mikepdiy/Macro-Keyboard-with-Encoders/Schematic/KB_Board_schematic.sch

## EAGLE design Schematic/KB_Board_schematic.sch (2021-04-27)

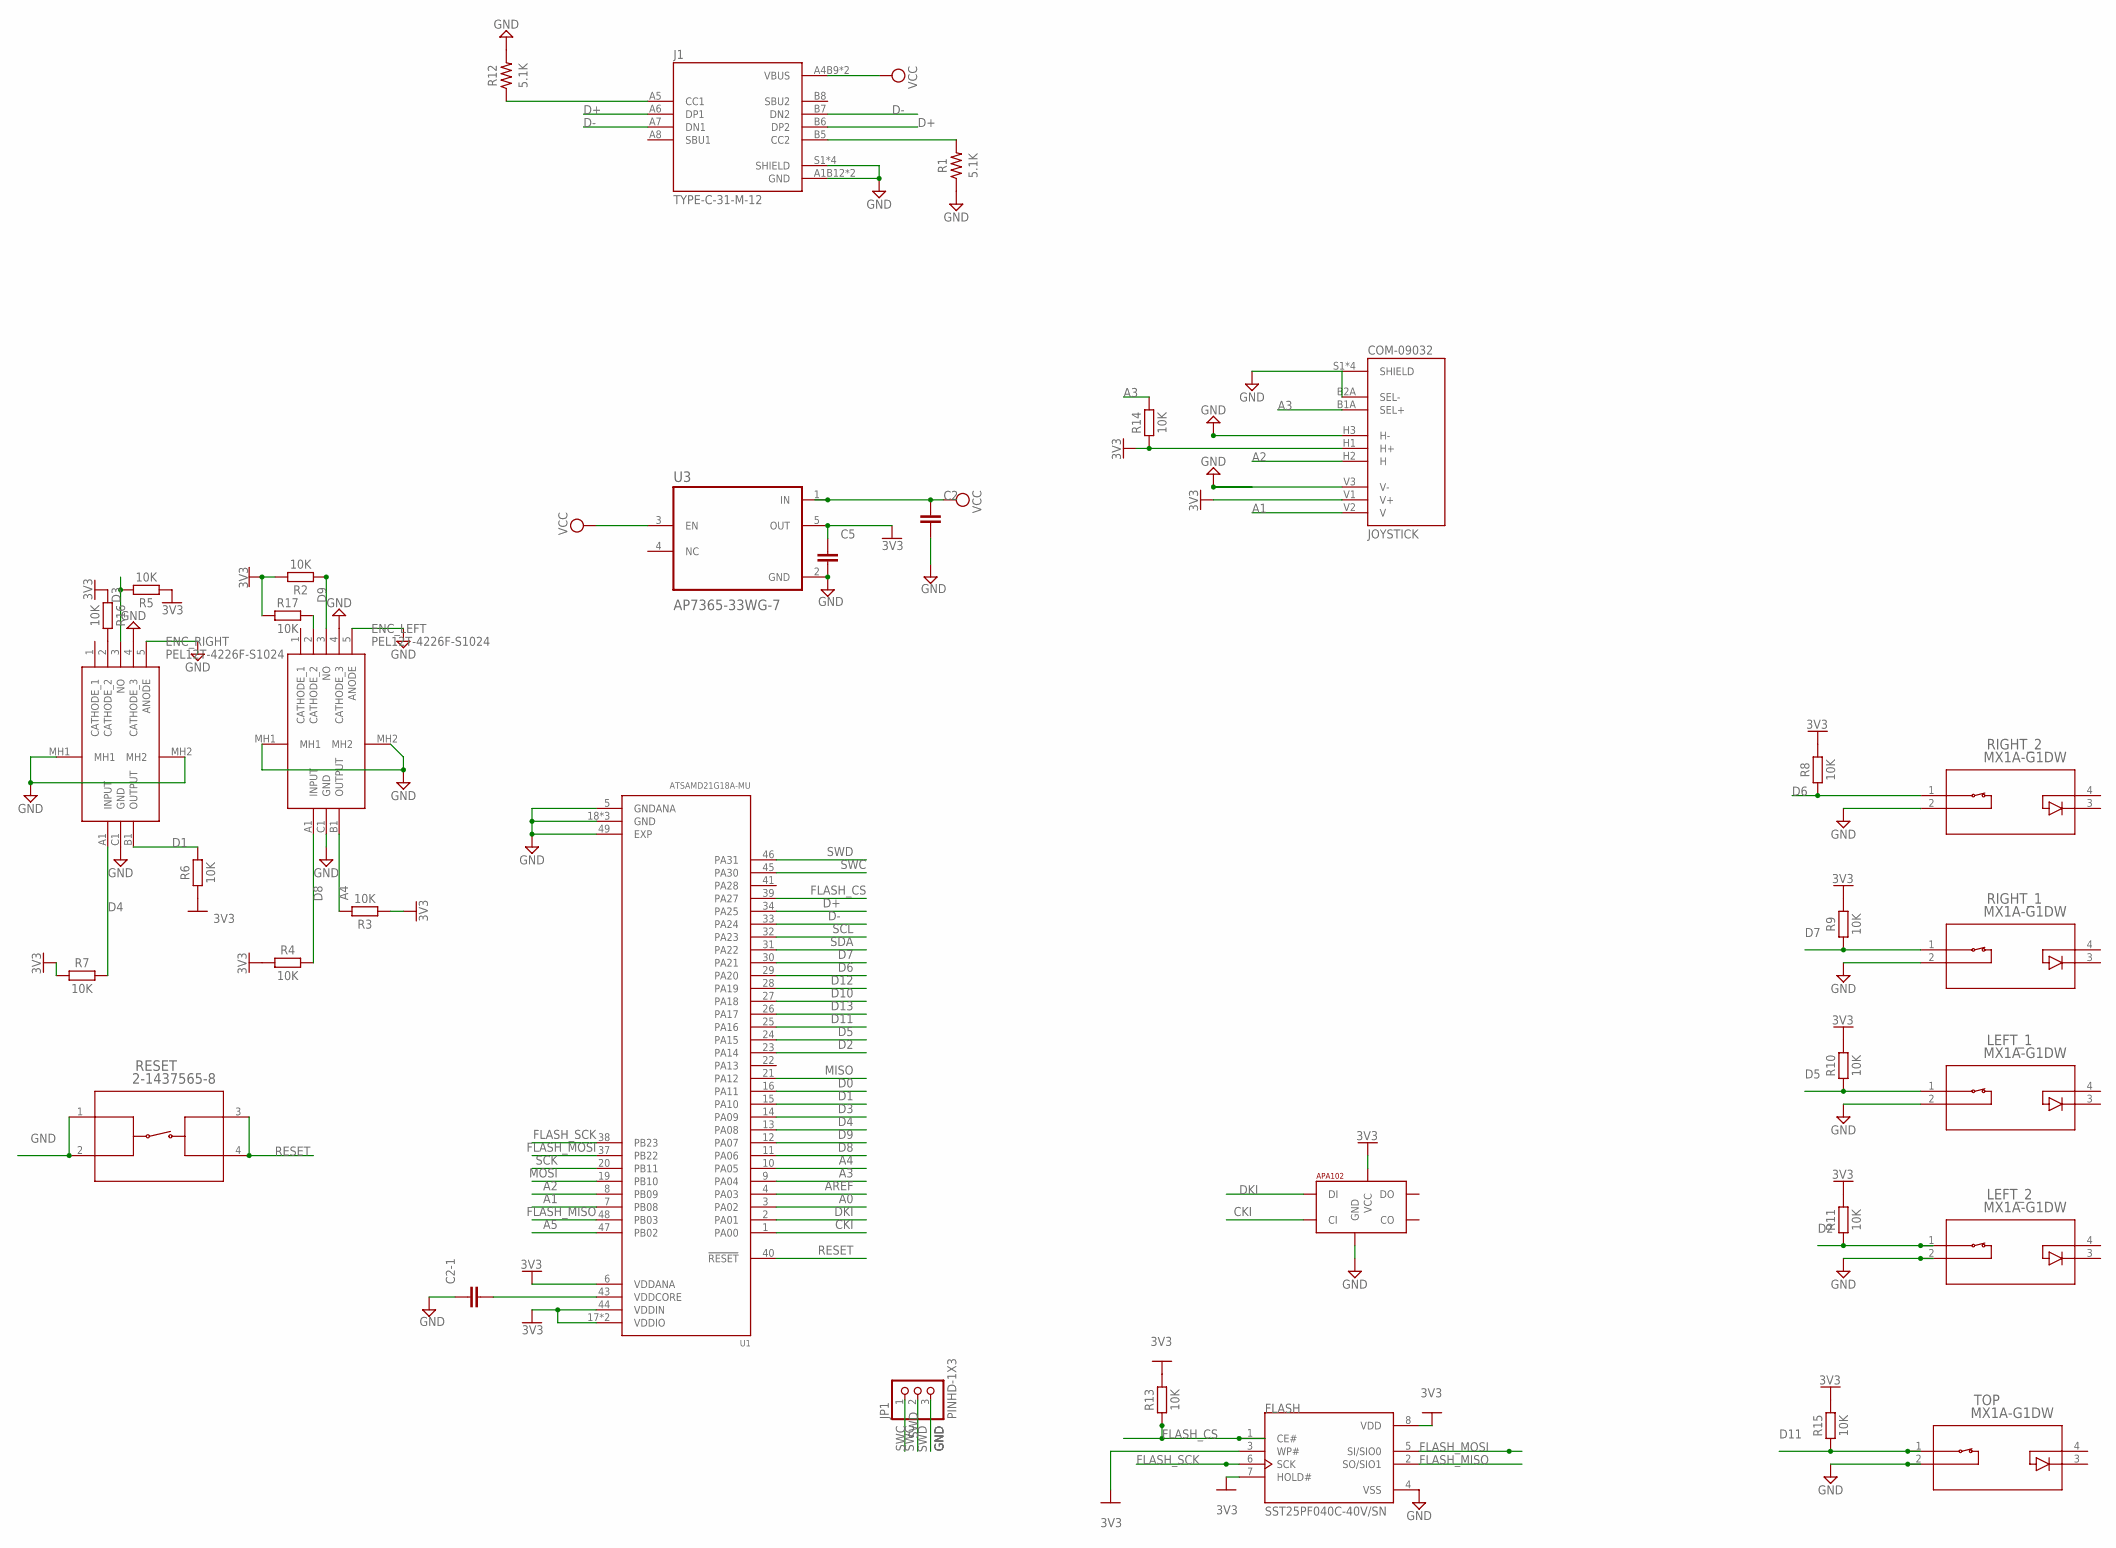
[picture p17: schematic KB_Board_schematic.sch]

Parts:
C2, C2-1, C5: C_CHIP-0805(2012-METRIC); CAPC2012X110
ENC_LEFT: PEL12T-4226F-S1024; PEL12T4226FS1024
ENC_RIGHT: PEL12T-4226F-S1024; PEL12T4226FS1024
FLASH: SST25PF040C-40V/SN; SOIC8
J1: TYPE-C-31-M-12; HRO_TYPE-C-31-M-12
JOYSTICK: COM-09032; XDCR_COM-09032
JP1: PINHD-1X3; 1X03
LEFT_1, LEFT_2: MX1A-G1DW; MX1A-G1DW_CHY
R1, R12: 5.1K; RESC1005X40
R2, R3, R4, R5, R6, R7, R8, R9, R10, R11, R13, R14, R15, R16, R17: 10K; RESC1608X60
RESET: 2-1437565-8; SW4_2-1437565-7
RIGHT_1, RIGHT_2: MX1A-G1DW; MX1A-G1DW_CHY
TOP: MX1A-G1DW; MX1A-G1DW_CHY
U1: ATSAMD21G18A-MU; QFN50P700X700X90-49N
U3: AP7365-33WG-7; SOT95P285X140-5N
U$1: APA1022020; APA102_2020

Connections:
3V3: C5.1, FLASH.3 (WP#), FLASH.7 (HOLD#), FLASH.8 (VDD), JOYSTICK.H1 (H+), JOYSTICK.V1 (V+), R2.2, R3.1, R4.1, R5.2, R6.1, R7.1, R8.2, R9.2, R10.2, R11.2, R13.2, R14.1, R15.2, R16.2, R17.2, U1.6 (VDDANA), U1.17 (VDDIO), U1.44 (VDDIN), U3.5 (OUT), U$1.V_CC (VCC)
A0: U1.3 (PA02)
A1: JOYSTICK.V2 (V), U1.7 (PB08)
A2: JOYSTICK.H2 (H), U1.8 (PB09)
A3: JOYSTICK.B1A (SEL+), R14.2, U1.9 (PA04)
A4: ENC_LEFT.B1 (OUTPUT), R3.2, U1.10 (PA05)
A5: U1.47 (PB02)
AREF: U1.4 (PA03)
CKI: U1.1 (PA00), U$1.C_IN (CI)
D0: U1.16 (PA11)
D1: ENC_RIGHT.B1 (OUTPUT), R6.2, U1.15 (PA10)
D2: LEFT_2.1, R11.1, U1.23 (PA14)
D3: ENC_RIGHT.3 (NO), R5.1, U1.14 (PA09)
D4: ENC_RIGHT.A1 (INPUT), R7.2, U1.13 (PA08)
D5: LEFT_1.1, R10.1, U1.24 (PA15)
D6: R8.1, RIGHT_2.1, U1.29 (PA20)
D7: R9.1, RIGHT_1.1, U1.30 (PA21)
D8: ENC_LEFT.A1 (INPUT), R4.2, U1.11 (PA06)
D9: ENC_LEFT.3 (NO), R2.1, U1.12 (PA07)
D10: U1.27 (PA18)
D11: R15.1, TOP.1, U1.25 (PA16)
D12: U1.28 (PA19)
D13: U1.26 (PA17)
D+: J1.A6 (DP1), J1.B6 (DP2), U1.34 (PA25)
D-: J1.A7 (DN1), J1.B7 (DN2), U1.33 (PA24)
DKI: U1.2 (PA01), U$1.D_IN (DI)
FLASH_CS: FLASH.1 (CE#), R13.1, U1.39 (PA27)
FLASH_MISO: FLASH.2 (SO/SIO1), U1.48 (PB03)
FLASH_MOSI: FLASH.5 (SI/SIO0), U1.37 (PB22)
FLASH_SCK: FLASH.6 (SCK), U1.38 (PB23)
GND: C2.2, C2-1.1, C5.2, ENC_LEFT.4 (CATHODE_3), ENC_LEFT.5 (ANODE), ENC_LEFT.C1 (GND), ENC_LEFT.MH1, ENC_LEFT.MH2, ENC_RIGHT.4 (CATHODE_3), ENC_RIGHT.5 (ANODE), ENC_RIGHT.C1 (GND), ENC_RIGHT.MH1, ENC_RIGHT.MH2, FLASH.4 (VSS), J1.A1B12 (GND), J1.S1 (SHIELD), JOYSTICK.B2A (SEL-), JOYSTICK.H3 (H-), JOYSTICK.S1 (SHIELD), JOYSTICK.V3 (V-), JP1.3, LEFT_1.2, LEFT_2.2, R1.1, R12.2, RESET.1, RESET.2, RIGHT_1.2, RIGHT_2.2, TOP.2, U1.5 (GNDANA), U1.18 (GND), U1.49 (EXP), U3.2 (GND), U$1.GND
MISO: U1.21 (PA12)
MOSI: U1.19 (PB10)
unnamed: C2-1.2, U1.43 (VDDCORE)
unnamed: J1.B5 (CC2), R1.2
unnamed: J1.A5 (CC1), R12.1
unnamed: ENC_RIGHT.2 (CATHODE_2), R16.1
unnamed: ENC_LEFT.2 (CATHODE_2), R17.1
RESET: RESET.3, RESET.4, U1.40 (!RESET)
SCK: U1.20 (PB11)
SCL: U1.32 (PA23)
SDA: U1.31 (PA22)
SWC: JP1.1, U1.45 (PA30)
SWD: JP1.2, U1.46 (PA31)
VCC: C2.1, J1.A4B9 (VBUS), U3.1 (IN), U3.3 (EN)
